nanbuwks/AKBONE2022/Arduino/sketchbook/akbone2022_terminal/akbone2022_terminal.ino

// AKBONE2022 AKBONE2022 Terminal
// 2022.11.19 K.Ohe New Create
#include "akbone.hpp"
//===========================================================
//	setup() ： arduino setup
//===========================================================
void setup() {
    akbone_setup();
}

//===========================================================
//	loop() ： arduino main loop
//===========================================================
void loop()
{
    akbone_terminal();
}
